jhagmar/keynjector/sw/keynjector/keynjector/src/cast128.c

/*
* Copyright 2014 Jonas Hagmar
*
* This file is part of keynjector.
*
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
* You should have received a copy of the GNU General Public License
* along with keynjector.  If not, see <http://www.gnu.org/licenses/>.
*/
#include <string.h>
#include "cast128.h"

static const uint32_t S1[];
static const uint32_t S2[];
static const uint32_t S3[];
static const uint32_t S4[];
static const uint32_t S5[];
static const uint32_t S6[];
static const uint32_t S7[];
static const uint32_t S8[];

#define B0(x) ((x) >> 24)
#define B1(x) (((x) >> 16) & 0xff)
#define B2(x) (((x) >> 8) & 0xff)
#define B3(x) ((x) & 0xff)

void cast128_init(cast128_ctx *ctx, uint8_t const key[CAST128_KEY_SIZE]) {
	uint32_t x[4];
	uint32_t z[4];

	x[0] = (key[ 0] << 24) | (key[ 1] << 16) | (key[ 2] << 8) | key[ 3];
	x[1] = (key[ 4] << 24) | (key[ 5] << 16) | (key[ 6] << 8) | key[ 7];
	x[2] = (key[ 8] << 24) | (key[ 9] << 16) | (key[10] << 8) | key[11];
	x[3] = (key[12] << 24) | (key[13] << 16) | (key[14] << 8) | key[15];

#define x0x1x2x3 (x[0])
#define x4x5x6x7 (x[1])
#define x8x9xAxB (x[2])
#define xCxDxExF (x[3])

#define z0z1z2z3 (z[0])
#define z4z5z6z7 (z[1])
#define z8z9zAzB (z[2])
#define zCzDzEzF (z[3])

#define x0 B0(x[0])
#define x1 B1(x[0])
#define x2 B2(x[0])
#define x3 B3(x[0])
#define x4 B0(x[1])
#define x5 B1(x[1])
#define x6 B2(x[1])
#define x7 B3(x[1])
#define x8 B0(x[2])
#define x9 B1(x[2])
#define xA B2(x[2])
#define xB B3(x[2])
#define xC B0(x[3])
#define xD B1(x[3])
#define xE B2(x[3])
#define xF B3(x[3])

#define z0 B0(z[0])
#define z1 B1(z[0])
#define z2 B2(z[0])
#define z3 B3(z[0])
#define z4 B0(z[1])
#define z5 B1(z[1])
#define z6 B2(z[1])
#define z7 B3(z[1])
#define z8 B0(z[2])
#define z9 B1(z[2])
#define zA B2(z[2])
#define zB B3(z[2])
#define zC B0(z[3])
#define zD B1(z[3])
#define zE B2(z[3])
#define zF B3(z[3])

	z0z1z2z3 = x0x1x2x3 ^ S5[xD] ^ S6[xF] ^ S7[xC] ^ S8[xE] ^ S7[x8];
	z4z5z6z7 = x8x9xAxB ^ S5[z0] ^ S6[z2] ^ S7[z1] ^ S8[z3] ^ S8[xA];
	z8z9zAzB = xCxDxExF ^ S5[z7] ^ S6[z6] ^ S7[z5] ^ S8[z4] ^ S5[x9];
	zCzDzEzF = x4x5x6x7 ^ S5[zA] ^ S6[z9] ^ S7[zB] ^ S8[z8] ^ S6[xB];
	ctx->Km[0] = S5[z8] ^ S6[z9] ^ S7[z7] ^ S8[z6] ^ S5[z2];
	ctx->Km[1] = S5[zA] ^ S6[zB] ^ S7[z5] ^ S8[z4] ^ S6[z6];
	ctx->Km[2] = S5[zC] ^ S6[zD] ^ S7[z3] ^ S8[z2] ^ S7[z9];
	ctx->Km[3] = S5[zE] ^ S6[zF] ^ S7[z1] ^ S8[z0] ^ S8[zC];
	x0x1x2x3 = z8z9zAzB ^ S5[z5] ^ S6[z7] ^ S7[z4] ^ S8[z6] ^ S7[z0];
	x4x5x6x7 = z0z1z2z3 ^ S5[x0] ^ S6[x2] ^ S7[x1] ^ S8[x3] ^ S8[z2];
	x8x9xAxB = z4z5z6z7 ^ S5[x7] ^ S6[x6] ^ S7[x5] ^ S8[x4] ^ S5[z1];
	xCxDxExF = zCzDzEzF ^ S5[xA] ^ S6[x9] ^ S7[xB] ^ S8[x8] ^ S6[z3];
	ctx->Km[4] = S5[x3] ^ S6[x2] ^ S7[xC] ^ S8[xD] ^ S5[x8];
	ctx->Km[5] = S5[x1] ^ S6[x0] ^ S7[xE] ^ S8[xF] ^ S6[xD];
	ctx->Km[6] = S5[x7] ^ S6[x6] ^ S7[x8] ^ S8[x9] ^ S7[x3];
	ctx->Km[7] = S5[x5] ^ S6[x4] ^ S7[xA] ^ S8[xB] ^ S8[x7];
	z0z1z2z3 = x0x1x2x3 ^ S5[xD] ^ S6[xF] ^ S7[xC] ^ S8[xE] ^ S7[x8];
	z4z5z6z7 = x8x9xAxB ^ S5[z0] ^ S6[z2] ^ S7[z1] ^ S8[z3] ^ S8[xA];
	z8z9zAzB = xCxDxExF ^ S5[z7] ^ S6[z6] ^ S7[z5] ^ S8[z4] ^ S5[x9];
	zCzDzEzF = x4x5x6x7 ^ S5[zA] ^ S6[z9] ^ S7[zB] ^ S8[z8] ^ S6[xB];
	ctx->Km[8] = S5[z3] ^ S6[z2] ^ S7[zC] ^ S8[zD] ^ S5[z9];
	ctx->Km[9] = S5[z1] ^ S6[z0] ^ S7[zE] ^ S8[zF] ^ S6[zC];
	ctx->Km[10] = S5[z7] ^ S6[z6] ^ S7[z8] ^ S8[z9] ^ S7[z2];
	ctx->Km[11] = S5[z5] ^ S6[z4] ^ S7[zA] ^ S8[zB] ^ S8[z6];
	x0x1x2x3 = z8z9zAzB ^ S5[z5] ^ S6[z7] ^ S7[z4] ^ S8[z6] ^ S7[z0];
	x4x5x6x7 = z0z1z2z3 ^ S5[x0] ^ S6[x2] ^ S7[x1] ^ S8[x3] ^ S8[z2];
	x8x9xAxB = z4z5z6z7 ^ S5[x7] ^ S6[x6] ^ S7[x5] ^ S8[x4] ^ S5[z1];
	xCxDxExF = zCzDzEzF ^ S5[xA] ^ S6[x9] ^ S7[xB] ^ S8[x8] ^ S6[z3];
	ctx->Km[12] = S5[x8] ^ S6[x9] ^ S7[x7] ^ S8[x6] ^ S5[x3];
	ctx->Km[13] = S5[xA] ^ S6[xB] ^ S7[x5] ^ S8[x4] ^ S6[x7];
	ctx->Km[14] = S5[xC] ^ S6[xD] ^ S7[x3] ^ S8[x2] ^ S7[x8];
	ctx->Km[15] = S5[xE] ^ S6[xF] ^ S7[x1] ^ S8[x0] ^ S8[xD];
	z0z1z2z3 = x0x1x2x3 ^ S5[xD] ^ S6[xF] ^ S7[xC] ^ S8[xE] ^ S7[x8];
	z4z5z6z7 = x8x9xAxB ^ S5[z0] ^ S6[z2] ^ S7[z1] ^ S8[z3] ^ S8[xA];
	z8z9zAzB = xCxDxExF ^ S5[z7] ^ S6[z6] ^ S7[z5] ^ S8[z4] ^ S5[x9];
	zCzDzEzF = x4x5x6x7 ^ S5[zA] ^ S6[z9] ^ S7[zB] ^ S8[z8] ^ S6[xB];
	ctx->Kr[0] = (uint8_t)((S5[z8] ^ S6[z9] ^ S7[z7] ^ S8[z6] ^ S5[z2]) & 0x1f);
	ctx->Kr[1] = (uint8_t)((S5[zA] ^ S6[zB] ^ S7[z5] ^ S8[z4] ^ S6[z6]) & 0x1f);
	ctx->Kr[2] = (uint8_t)((S5[zC] ^ S6[zD] ^ S7[z3] ^ S8[z2] ^ S7[z9]) & 0x1f);
	ctx->Kr[3] = (uint8_t)((S5[zE] ^ S6[zF] ^ S7[z1] ^ S8[z0] ^ S8[zC]) & 0x1f);
	x0x1x2x3 = z8z9zAzB ^ S5[z5] ^ S6[z7] ^ S7[z4] ^ S8[z6] ^ S7[z0];
	x4x5x6x7 = z0z1z2z3 ^ S5[x0] ^ S6[x2] ^ S7[x1] ^ S8[x3] ^ S8[z2];
	x8x9xAxB = z4z5z6z7 ^ S5[x7] ^ S6[x6] ^ S7[x5] ^ S8[x4] ^ S5[z1];
	xCxDxExF = zCzDzEzF ^ S5[xA] ^ S6[x9] ^ S7[xB] ^ S8[x8] ^ S6[z3];
	ctx->Kr[4] = (uint8_t)((S5[x3] ^ S6[x2] ^ S7[xC] ^ S8[xD] ^ S5[x8]) & 0x1f);
	ctx->Kr[5] = (uint8_t)((S5[x1] ^ S6[x0] ^ S7[xE] ^ S8[xF] ^ S6[xD]) & 0x1f);
	ctx->Kr[6] = (uint8_t)((S5[x7] ^ S6[x6] ^ S7[x8] ^ S8[x9] ^ S7[x3]) & 0x1f);
	ctx->Kr[7] = (uint8_t)((S5[x5] ^ S6[x4] ^ S7[xA] ^ S8[xB] ^ S8[x7]) & 0x1f);
	z0z1z2z3 = x0x1x2x3 ^ S5[xD] ^ S6[xF] ^ S7[xC] ^ S8[xE] ^ S7[x8];
	z4z5z6z7 = x8x9xAxB ^ S5[z0] ^ S6[z2] ^ S7[z1] ^ S8[z3] ^ S8[xA];
	z8z9zAzB = xCxDxExF ^ S5[z7] ^ S6[z6] ^ S7[z5] ^ S8[z4] ^ S5[x9];
	zCzDzEzF = x4x5x6x7 ^ S5[zA] ^ S6[z9] ^ S7[zB] ^ S8[z8] ^ S6[xB];
	ctx->Kr[8] = (uint8_t)((S5[z3] ^ S6[z2] ^ S7[zC] ^ S8[zD] ^ S5[z9]) & 0x1f);
	ctx->Kr[9] = (uint8_t)((S5[z1] ^ S6[z0] ^ S7[zE] ^ S8[zF] ^ S6[zC]) & 0x1f);
	ctx->Kr[10] = (uint8_t)((S5[z7] ^ S6[z6] ^ S7[z8] ^ S8[z9] ^ S7[z2]) & 0x1f);
	ctx->Kr[11] = (uint8_t)((S5[z5] ^ S6[z4] ^ S7[zA] ^ S8[zB] ^ S8[z6]) & 0x1f);
	x0x1x2x3 = z8z9zAzB ^ S5[z5] ^ S6[z7] ^ S7[z4] ^ S8[z6] ^ S7[z0];
	x4x5x6x7 = z0z1z2z3 ^ S5[x0] ^ S6[x2] ^ S7[x1] ^ S8[x3] ^ S8[z2];
	x8x9xAxB = z4z5z6z7 ^ S5[x7] ^ S6[x6] ^ S7[x5] ^ S8[x4] ^ S5[z1];
	xCxDxExF = zCzDzEzF ^ S5[xA] ^ S6[x9] ^ S7[xB] ^ S8[x8] ^ S6[z3];
	ctx->Kr[12] = (uint8_t)((S5[x8] ^ S6[x9] ^ S7[x7] ^ S8[x6] ^ S5[x3]) & 0x1f);
	ctx->Kr[13] = (uint8_t)((S5[xA] ^ S6[xB] ^ S7[x5] ^ S8[x4] ^ S6[x7]) & 0x1f);
	ctx->Kr[14] = (uint8_t)((S5[xC] ^ S6[xD] ^ S7[x3] ^ S8[x2] ^ S7[x8]) & 0x1f);
	ctx->Kr[15] = (uint8_t)((S5[xE] ^ S6[xF] ^ S7[x1] ^ S8[x0] ^ S8[xD]) & 0x1f);
}

#define ROTL(x, n) (((x) << (n)) | ((x) >> (32 - (n))))

#define	F1(X, D, Km, Kr) { \
	I = ROTL((Km) + (D), (Kr)); \
	(X) ^= ((S1[B0(I)] ^ S2[B1(I)]) - S3[B2(I)]) + S4[B3(I)]; \
}

#define	F2(X, D, Km, Kr) { \
	I = ROTL((Km) ^ (D), (Kr)); \
	(X) ^= ((S1[B0(I)] - S2[B1(I)]) + S3[B2(I)]) ^ S4[B3(I)]; \
}

#define	F3(X, D, Km, Kr) { \
	I = ROTL((Km) - (D), (Kr)); \
	(X) ^= ((S1[B0(I)] + S2[B1(I)]) ^ S3[B2(I)]) - S4[B3(I)]; \
}


void cast128_encrypt(cast128_ctx *ctx, uint8_t c[CAST128_BLOCK_SIZE], uint8_t const m[CAST128_BLOCK_SIZE]) {

	uint32_t L, R, I;

	L = (m[0] << 24) | (m[1] << 16) | (m[2] << 8) | m[3];
	R = (m[4] << 24) | (m[5] << 16) | (m[6] << 8) | m[7];

	F1(L, R, ctx->Km[0], ctx->Kr[0]);
	F2(R, L, ctx->Km[1], ctx->Kr[1]);
	F3(L, R, ctx->Km[2], ctx->Kr[2]);
	F1(R, L, ctx->Km[3], ctx->Kr[3]);
	F2(L, R, ctx->Km[4], ctx->Kr[4]);
	F3(R, L, ctx->Km[5], ctx->Kr[5]);
	F1(L, R, ctx->Km[6], ctx->Kr[6]);
	F2(R, L, ctx->Km[7], ctx->Kr[7]);
	F3(L, R, ctx->Km[8], ctx->Kr[8]);
	F1(R, L, ctx->Km[9], ctx->Kr[9]);
	F2(L, R, ctx->Km[10], ctx->Kr[10]);
	F3(R, L, ctx->Km[11], ctx->Kr[11]);
	F1(L, R, ctx->Km[12], ctx->Kr[12]);
	F2(R, L, ctx->Km[13], ctx->Kr[13]);
	F3(L, R, ctx->Km[14], ctx->Kr[14]);
	F1(R, L, ctx->Km[15], ctx->Kr[15]);

	c[0] = (R >> 24) & 0xff;
	c[1] = (R >> 16) & 0xff;
	c[2] = (R >> 8) & 0xff;
	c[3] = R & 0xff;
	c[4] = (L >> 24) & 0xff;
	c[5] = (L >> 16) & 0xff;
	c[6] = (L >> 8) & 0xff;
	c[7] = L & 0xff;
}

static uint8_t test_key[CAST128_KEY_SIZE] = {
		0x01, 0x23, 0x45, 0x67, 0x12, 0x34, 0x56, 0x78,
		0x23, 0x45, 0x67, 0x89, 0x34, 0x56, 0x78, 0x9A
};

static uint8_t plain[CAST128_BLOCK_SIZE] = {
		0x01, 0x23, 0x45, 0x67, 0x89, 0xAB, 0xCD, 0xEF
};

static uint8_t check[CAST128_BLOCK_SIZE] = {
		0x23, 0x8B, 0x4F, 0xE5, 0x84, 0x7E, 0x44, 0xB2
};

static uint8_t const a_init[2 * CAST128_BLOCK_SIZE] = {
		0x01, 0x23, 0x45, 0x67, 0x12, 0x34, 0x56, 0x78,
		0x23, 0x45, 0x67, 0x89, 0x34, 0x56, 0x78, 0x9A
};

static uint8_t const b_init[2 * CAST128_BLOCK_SIZE] = {
		0x01, 0x23, 0x45, 0x67, 0x12, 0x34, 0x56, 0x78,
		0x23, 0x45, 0x67, 0x89, 0x34, 0x56, 0x78, 0x9A
};

static uint8_t const a_final[2 * CAST128_BLOCK_SIZE] = {
		0xEE, 0xA9, 0xD0, 0xA2, 0x49, 0xFD, 0x3B, 0xA6,
		0xB3, 0x43, 0x6F, 0xB8, 0x9D, 0x6D, 0xCA, 0x92
};

static uint8_t const b_final[2 * CAST128_BLOCK_SIZE] = {
		0xB2, 0xC9, 0x5E, 0xB0, 0x0C, 0x31, 0xAD, 0x71,
		0x80, 0xAC, 0x05, 0xB8, 0xE8, 0x3D, 0x69, 0x6E
};

static void encrypt(uint8_t c[CAST128_BLOCK_SIZE], uint8_t const m[CAST128_BLOCK_SIZE], uint8_t const key[CAST128_KEY_SIZE]) {
	cast128_ctx ctx;

	cast128_init(&ctx, key);
	cast128_encrypt(&ctx, c, m);
}

void cast128_cfb_reinit(cast128_cfb_ctx *ctx, uint8_t const iv[CAST128_BLOCK_SIZE]) {
	if (iv) {
		memcpy(ctx->fr, iv, 8);
	}
	else {
		memset(ctx->fr, 0, 8);
	}
	ctx->n = 8;
}

void cast128_cfb_init(cast128_cfb_ctx *ctx, uint8_t const key[CAST128_KEY_SIZE], uint8_t const iv[CAST128_BLOCK_SIZE]) {
	cast128_init(&(ctx->ctx), key);
	cast128_cfb_reinit(ctx, iv);
}

void cast128_cfb_decrypt(cast128_cfb_ctx *ctx, uint8_t *m, uint8_t const *c, uint32_t len) {

	for ( ; ((ctx->n < 8) && len); ctx->n++, len--) {

		ctx->fr[ctx->n] = *c;
		*m++ = *c++ ^ ctx->fre[ctx->n];

	}

	while (len >= 8) {
		cast128_encrypt(&(ctx->ctx), ctx->fre, ctx->fr);
		ctx->fr[0] = c[0];
		m[0] = c[0] ^ ctx->fre[0];
		ctx->fr[1] = c[1];
		m[1] = c[1] ^ ctx->fre[1];
		ctx->fr[2] = c[2];
		m[2] = c[2] ^ ctx->fre[2];
		ctx->fr[3] = c[3];
		m[3] = c[3] ^ ctx->fre[3];
		ctx->fr[4] = c[4];
		m[4] = c[4] ^ ctx->fre[4];
		ctx->fr[5] = c[5];
		m[5] = c[5] ^ ctx->fre[5];
		ctx->fr[6] = c[6];
		m[6] = c[6] ^ ctx->fre[6];
		ctx->fr[7] = c[7];
		m[7] = c[7] ^ ctx->fre[7];
		len -= 8;
		m += 8;
		c += 8;
	}

	if (len > 0) {
		cast128_encrypt(&(ctx->ctx), ctx->fre, ctx->fr);
		switch (len) {
		case 7:
			ctx->fr[6] = c[6];
			m[6] = c[6] ^ ctx->fre[6];
		case 6:
			ctx->fr[5] = c[5];
			m[5] = c[5] ^ ctx->fre[5];
		case 5:
			ctx->fr[4] = c[4];
			m[4] = c[4] ^ ctx->fre[4];
		case 4:
			ctx->fr[3] = c[3];
			m[3] = c[3] ^ ctx->fre[3];
		case 3:
			ctx->fr[2] = c[2];
			m[2] = c[2] ^ ctx->fre[2];
		case 2:
			ctx->fr[1] = c[1];
			m[1] = c[1] ^ ctx->fre[1];
		case 1:
			ctx->fr[0] = c[0];
			m[0] = c[0] ^ ctx->fre[0];
		}
		ctx->n = len;
	}
}

int cast128_test(void) {

	int i;
	uint8_t r[CAST128_BLOCK_SIZE];
	uint8_t a[2 * CAST128_BLOCK_SIZE], b[2 * CAST128_BLOCK_SIZE];

	encrypt(r, plain, test_key);
	if (memcmp(r, check, 8) != 0) return 0;

#define aL (a)
#define aR (&a[CAST128_BLOCK_SIZE])
#define bL (b)
#define bR (&b[CAST128_BLOCK_SIZE])

	memcpy(a, a_init, 2 * CAST128_BLOCK_SIZE);
	memcpy(b, b_init, 2 * CAST128_BLOCK_SIZE);

	for (i = 0; i < 1000000; i++) {
		encrypt(aL, aL, b);
		encrypt(aR, aR, b);
		encrypt(bL, bL, a);
		encrypt(bR, bR, a);
	}

#undef aL
#undef aR
#undef bL
#undef bR

	return ((memcmp(a, a_final, 2 * CAST128_BLOCK_SIZE) == 0) && (memcmp(b, b_final, 2 * CAST128_BLOCK_SIZE) == 0));

}

static const uint32_t S1[256] = { 0x30fb40d4, 0x9fa0ff0b, 0x6beccd2f,
		0x3f258c7a, 0x1e213f2f, 0x9c004dd3, 0x6003e540, 0xcf9fc949, 0xbfd4af27,
		0x88bbbdb5, 0xe2034090, 0x98d09675, 0x6e63a0e0, 0x15c361d2, 0xc2e7661d,
		0x22d4ff8e, 0x28683b6f, 0xc07fd059, 0xff2379c8, 0x775f50e2, 0x43c340d3,
		0xdf2f8656, 0x887ca41a, 0xa2d2bd2d, 0xa1c9e0d6, 0x346c4819, 0x61b76d87,
		0x22540f2f, 0x2abe32e1, 0xaa54166b, 0x22568e3a, 0xa2d341d0, 0x66db40c8,
		0xa784392f, 0x004dff2f, 0x2db9d2de, 0x97943fac, 0x4a97c1d8, 0x527644b7,
		0xb5f437a7, 0xb82cbaef, 0xd751d159, 0x6ff7f0ed, 0x5a097a1f, 0x827b68d0,
		0x90ecf52e, 0x22b0c054, 0xbc8e5935, 0x4b6d2f7f, 0x50bb64a2, 0xd2664910,
		0xbee5812d, 0xb7332290, 0xe93b159f, 0xb48ee411, 0x4bff345d, 0xfd45c240,
		0xad31973f, 0xc4f6d02e, 0x55fc8165, 0xd5b1caad, 0xa1ac2dae, 0xa2d4b76d,
		0xc19b0c50, 0x882240f2, 0x0c6e4f38, 0xa4e4bfd7, 0x4f5ba272, 0x564c1d2f,
		0xc59c5319, 0xb949e354, 0xb04669fe, 0xb1b6ab8a, 0xc71358dd, 0x6385c545,
		0x110f935d, 0x57538ad5, 0x6a390493, 0xe63d37e0, 0x2a54f6b3, 0x3a787d5f,
		0x6276a0b5, 0x19a6fcdf, 0x7a42206a, 0x29f9d4d5, 0xf61b1891, 0xbb72275e,
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
		0xe139673b, 0xefa63fb8, 0x71873054, 0xb6f2cf3b, 0x9f326442, 0xcb15a4cc,
		0xb01a4504, 0xf1e47d8d, 0x844a1be5, 0xbae7dfdc, 0x42cbda70, 0xcd7dae0a,
		0x57e85b7a, 0xd53f5af6, 0x20cf4d8c, 0xcea4d428, 0x79d130a4, 0x3486ebfb,
		0x33d3cddc, 0x77853b53, 0x37effcb5, 0xc5068778, 0xe580b3e6, 0x4e68b8f4,
		0xc5c8b37e, 0x0d809ea2, 0x398feb7c, 0x132a4f94, 0x43b7950e, 0x2fee7d1c,
		0x223613bd, 0xdd06caa2, 0x37df932b, 0xc4248289, 0xacf3ebc3, 0x5715f6b7,
		0xef3478dd, 0xf267616f, 0xc148cbe4, 0x9052815e, 0x5e410fab, 0xb48a2465,
		0x2eda7fa4, 0xe87b40e4, 0xe98ea084, 0x5889e9e1, 0xefd390fc, 0xdd07d35b,
		0xdb485694, 0x38d7e5b2, 0x57720101, 0x730edebc, 0x5b643113, 0x94917e4f,
		0x503c2fba, 0x646f1282, 0x7523d24a, 0xe0779695, 0xf9c17a8f, 0x7a5b2121,
		0xd187b896, 0x29263a4d, 0xba510cdf, 0x81f47c9f, 0xad1163ed, 0xea7b5965,
		0x1a00726e, 0x11403092, 0x00da6d77, 0x4a0cdd61, 0xad1f4603, 0x605bdfb0,
		0x9eedc364, 0x22ebe6a8, 0xcee7d28a, 0xa0e736a0, 0x5564a6b9, 0x10853209,
		0xc7eb8f37, 0x2de705ca, 0x8951570f, 0xdf09822b, 0xbd691a6c, 0xaa12e4f2,
		0x87451c0f, 0xe0f6a27a, 0x3ada4819, 0x4cf1764f, 0x0d771c2b, 0x67cdb156,
		0x350d8384, 0x5938fa0f, 0x42399ef3, 0x36997b07, 0x0e84093d, 0x4aa93e61,
		0x8360d87b, 0x1fa98b0c, 0x1149382c, 0xe97625a5, 0x0614d1b7, 0x0e25244b,
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
