jhagmar/keynjector/sw/keynjector_ui/keynjector_ui/ui_data.h

static const struct {
	unsigned char r;
	unsigned char g;
	unsigned char b;
} bg[LCD_HEIGHT] = {
{30, 87, 153}, {30, 87, 153}, {30, 88, 153}, {31, 88, 154}, {31, 88, 154}, {31, 88, 154}, {31, 89, 154}, {31, 89, 155}, {32, 89, 155}, {32, 89, 155}, {32, 90, 155}, 
{32, 90, 156}, {32, 90, 156}, {32, 90, 156}, {33, 91, 156}, {33, 91, 157}, {33, 91, 157}, {33, 91, 157}, {33, 92, 157}, {34, 92, 158}, {34, 92, 158}, {34, 92, 158}, 
{34, 93, 158}, {34, 93, 158}, {35, 93, 159}, {35, 93, 159}, {35, 94, 159}, {35, 94, 159}, {35, 94, 160}, {36, 94, 160}, {36, 95, 160}, {36, 95, 160}, {36, 95, 161}, 
{36, 95, 161}, {36, 96, 161}, {37, 96, 161}, {37, 96, 162}, {37, 96, 162}, {37, 97, 162}, {37, 97, 162}, {38, 97, 163}, {38, 98, 163}, {38, 98, 163}, {38, 98, 163}, 
{38, 98, 163}, {39, 99, 164}, {39, 99, 164}, {39, 99, 164}, {39, 99, 164}, {39, 100, 165}, {40, 100, 165}, {40, 100, 165}, {40, 100, 165}, {40, 101, 166}, {40, 101, 166}, 
{40, 101, 166}, {41, 101, 166}, {41, 102, 167}, {41, 102, 167}, {41, 102, 167}, {41, 102, 167}, {42, 103, 167}, {42, 103, 168}, {42, 103, 168}, {42, 103, 168}, {42, 104, 168}, 
{43, 104, 169}, {43, 104, 169}, {43, 104, 169}, {43, 105, 169}, {43, 105, 170}, {44, 105, 170}, {44, 105, 170}, {44, 106, 170}, {44, 106, 171}, {44, 106, 171}, {44, 106, 171}, 
{45, 107, 171}, {45, 107, 172}, {45, 107, 172}, {45, 108, 172}, {45, 108, 172}, {46, 108, 172}, {46, 108, 173}, {46, 109, 173}, {46, 109, 173}, {46, 109, 173}, {47, 109, 174}, 
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
254, 2, 157, 0, 4, 23, 254, 3, 253, 117, 0, 8, 254, 2, 157, 0, 3, 113, 254, 3, 241, 3, 0, 9, 254, 2, 157, 1, 17, 241, 254, 3, 151, 0, 11, 254, 2, 157, 93, 254, 3, 
243, 15, 0, 12, 254, 6, 177, 0, 14, 254, 4, 249, 37, 0, 15, 254, 3, 193, 0, 17, 147, 255, 61, 0, 18, }
};
