jhagmar/keynjector/sw/keynjector_ui/keynjector_ui/stdafx.cpp

// stdafx.cpp : source file that includes just the standard includes
// keynjector_ui.pch will be the pre-compiled header
// stdafx.obj will contain the pre-compiled type information

#include "stdafx.h"

// TODO: reference any additional headers you need in STDAFX.H
// and not in this file
